skhg/raspberrypi-killswitch/images/IMG_2515.jpeg

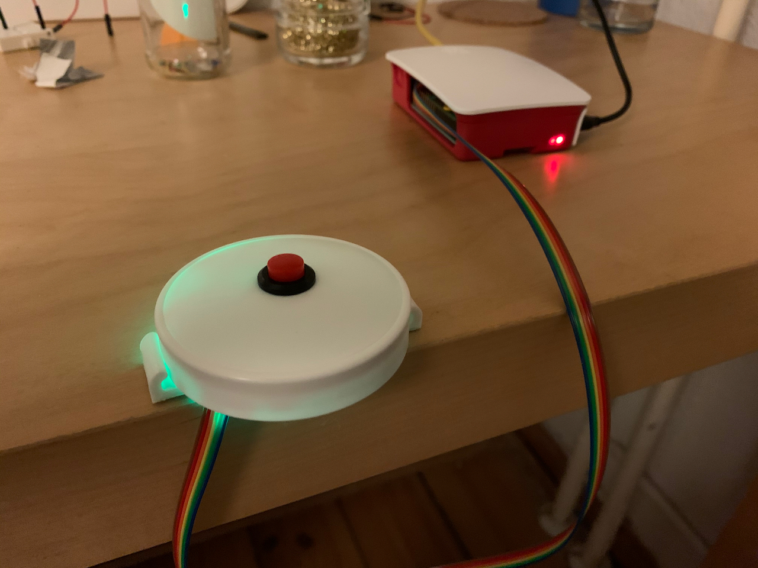
images/IMG_2515.jpeg
